Lodigolden/business_card/fw/business_card_fw/src/config.h

#ifndef CONFIG_H
#define CONFIG_H

////////////////////////////////////////////////////////////////////////////////////////////////////
// Include(s)
////////////////////////////////////////////////////////////////////////////////////////////////////
#include <xc.h>

////////////////////////////////////////////////////////////////////////////////////////////////////
/// @brief Configures the MCU initial state.
////////////////////////////////////////////////////////////////////////////////////////////////////
void config(void);

#endif // CONFIG_H
